vektorious/hpi_smart_plants/img/moisture+pump+i2c_circuit_bb.png

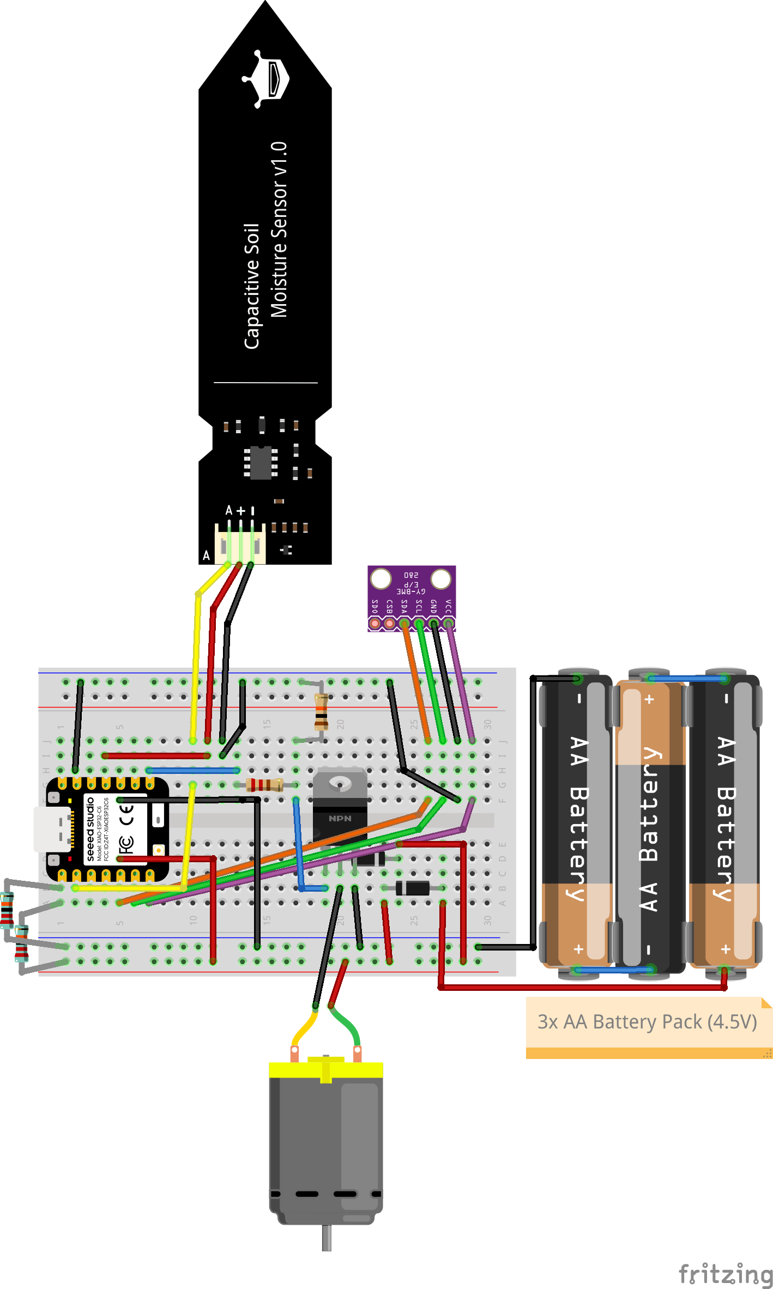
img/moisture+pump+i2c_circuit_bb.png
