vektorious/hpi_smart_plants/img/moisture+pump+i2c_circuit_lipo_bb.png

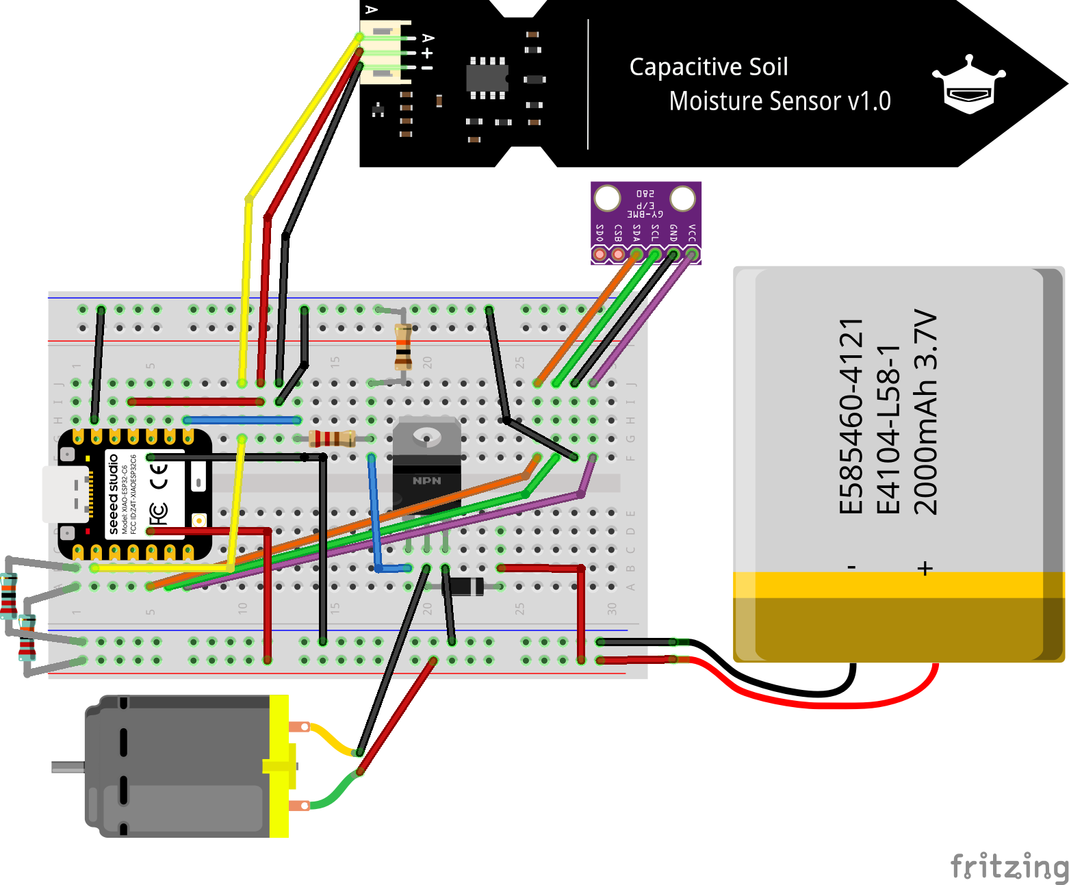
img/moisture+pump+i2c_circuit_lipo_bb.png
