vektorious/hpi_smart_plants/hardware/3d-print/src/light_sensor_bottom.3mf

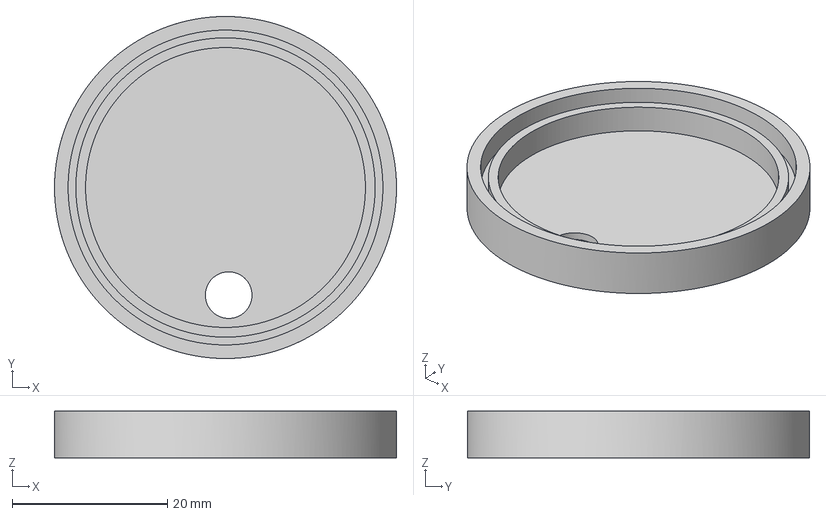
[picture p29: CAD file, 2025-11-18]
hardware/3d-print/src/light_sensor_bottom.3mf
44.0 x 44.0 x 6.00 mm
