vektorious/hpi_smart_plants/hardware/3d-print/bme_housing/thread_scaled.stl

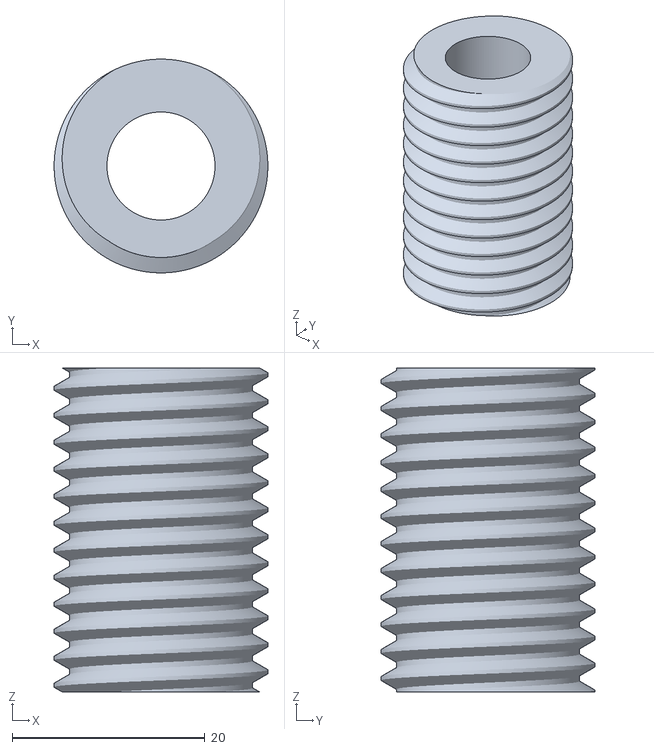
[picture p30: CAD file, 2025-11-18]
hardware/3d-print/bme_housing/thread_scaled.stl
22.2 x 22.2 x 33.6
