vektorious/hpi_smart_plants/hardware/3d-print/pump/pump_housing-Bottom_large.obj

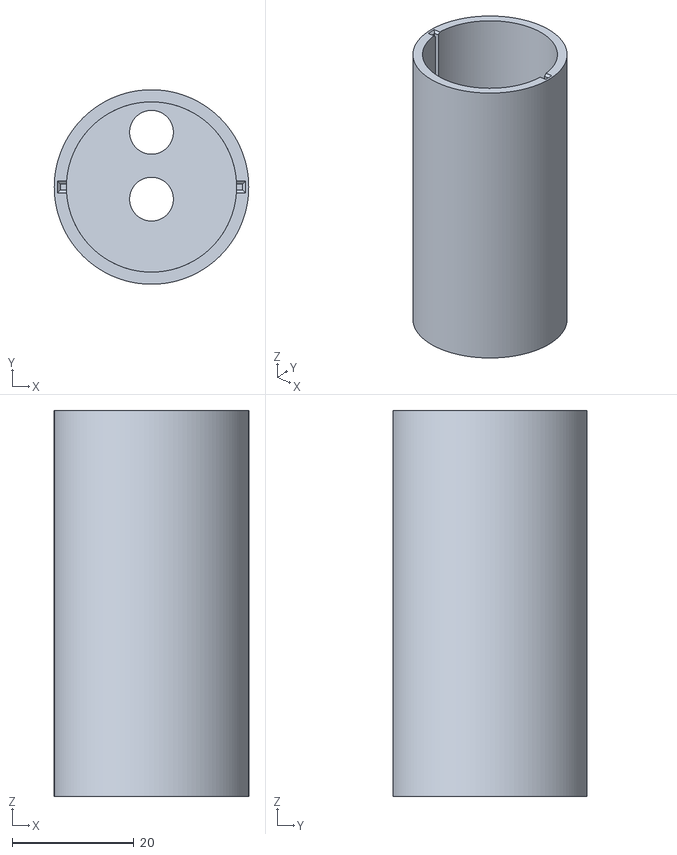
[picture p31: CAD file, 2025-11-18]
hardware/3d-print/pump/pump_housing-Bottom_large.obj
32.0 x 32.0 x 63.5
