vektorious/hpi_smart_plants/hardware/3d-print/src/ring.3mf

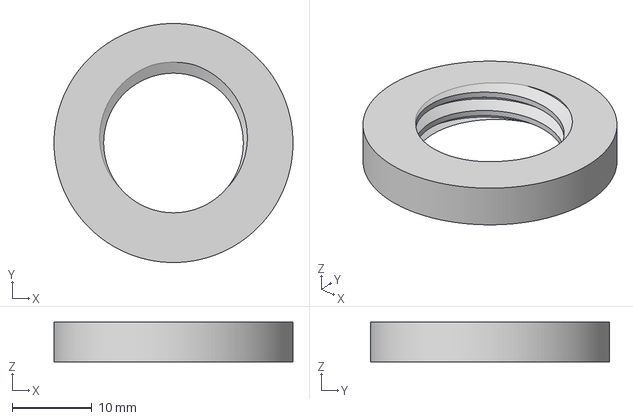
[picture p32: CAD file, 2025-11-18]
hardware/3d-print/src/ring.3mf
30.0 x 30.0 x 5.00 mm
