vektorious/hpi_smart_plants/hardware/3d-print/src/tube.3mf

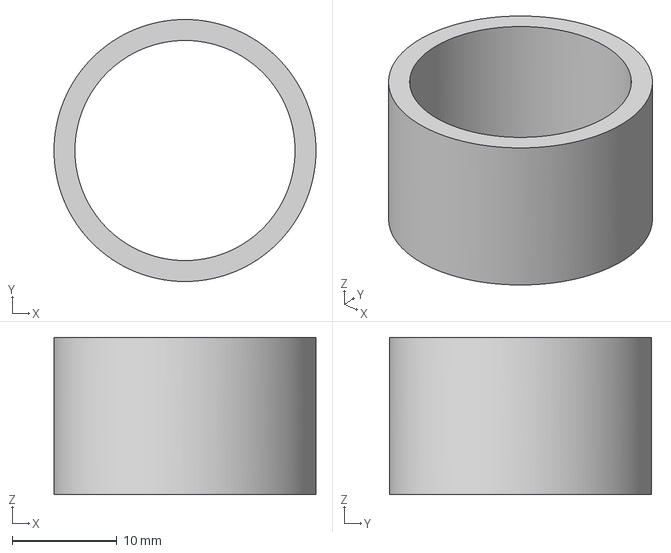
[picture p33: CAD file, 2025-11-18]
hardware/3d-print/src/tube.3mf
25.0 x 25.0 x 15.0 mm
