vektorious/hpi_smart_plants/code/sp_modular/battery.ino

float readBatteryVoltage() {
  analogReadMilliVolts(PIN_BATTERY); // discard first noisy sample
  delay(50);
  uint32_t v = 0;
  for (int i = 0; i < 16; i++) {
    v += analogReadMilliVolts(PIN_BATTERY);
  }
  return settings.battDivider * (v / 16.0) / 1000.0;
}
